jmlaulhe/LAUDS/04_hardware/02_sources_media/img/photo_61_2025-10-27_17-47-01.jpg

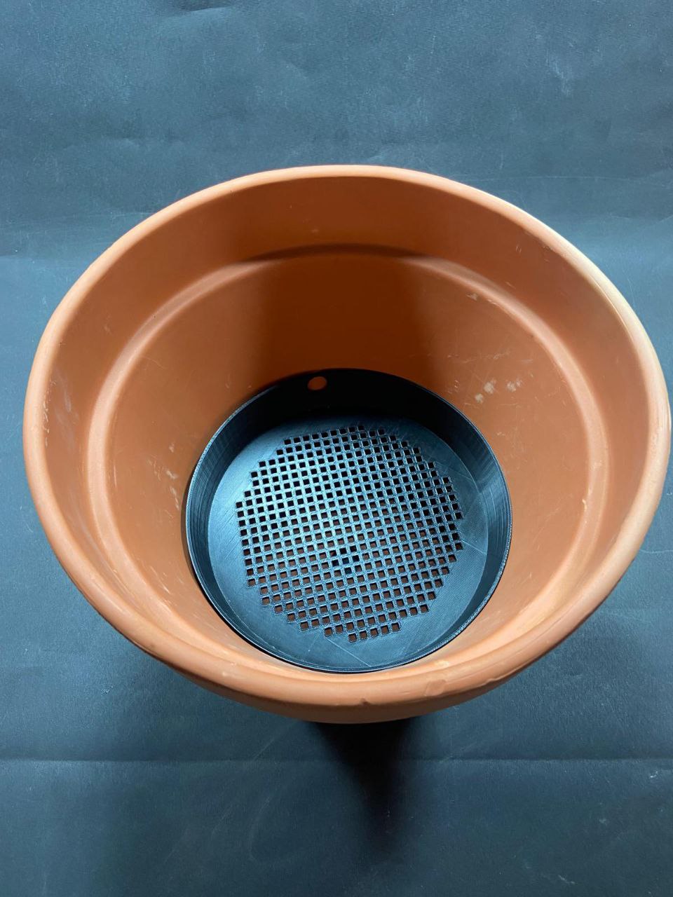
04_hardware/02_sources_media/img/photo_61_2025-10-27_17-47-01.jpg
